EmbarcaTech-2025/projeto-final-antonio_carlos_ricardo/DesenvolvimentoDoProjeto/Fase3/Code/Decode/README.md

# Example:

$ java Decode **07994509EF247AF4976157E876D9C710E1**
- Byte de Controle (BC): 0x07
- Battery: 76.5 %
- Umidade: 34.5 %
- Temperatura: 25.43 °C
- Pressão: 1013.24 hPa
- Latitude: -22.817343 graus
- Longitude: -47.07148 graus
- Altitude: 432.1 m
