EmbarcaTech-2025/projeto-final-antonio_carlos_ricardo/DesenvolvimentoDoProjeto/Fase3/Etapa4/Apresentação 0202.pdf

## Estação Meteorológica IoT

Etapa 4 – Semana 4 – Contexto

- Projeto de estação meteorológica IoT de baixo consumo
- Implantação prevista de 10 unidades no campus
- Comunicação via LoRaWAN
- Backend com TTN e ThingsBoard
- Objetivo da Etapa 4: validação, consolidação e pré-entrega

## Estação Meteorológica IoT

Arquitetura Geral do Sistema

- Nó sensor com microcontrolador RP2040
- Sensores (temperatura, umidade, pressão, GPS)
- Medição de bateria e temperatura do MPU
- Alimentação solar
- Comunicação LoRaWAN
- Gateway FEEC → TTN → ThingsBoard

Arquitetura Geral do Sistema

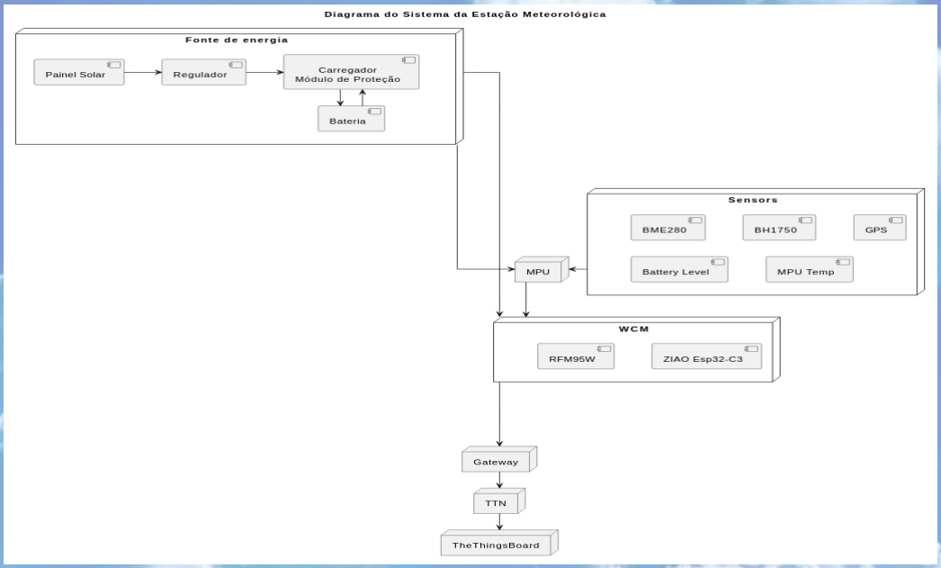
[picture p67: figure]

## Estação Meteorológica IoT

Objetivos e Escopo da Etapa 4

- Validar tecnicamente o protótipo
- Realizar validação externa inicial
- Incorporar feedback técnico e funcional
- Consolidar documentação do projeto
- Preparar o sistema para implantação em campo

## Estação Meteorológica IoT

Validação Técnica e Externa

- Validação técnica interna dos subsistemas
- Testes integrados de sensores, energia e comunicação
- Demonstração do sistema a avaliadores externos

## Estação Meteorológica IoT

Ajustes Realizados no Sistema

- Otimização do payload LoRaWAN
- Melhoria de logs e diagnósticos
- Revisão do gerenciamento energético
- Migração para placa dedicada (PCB própria)

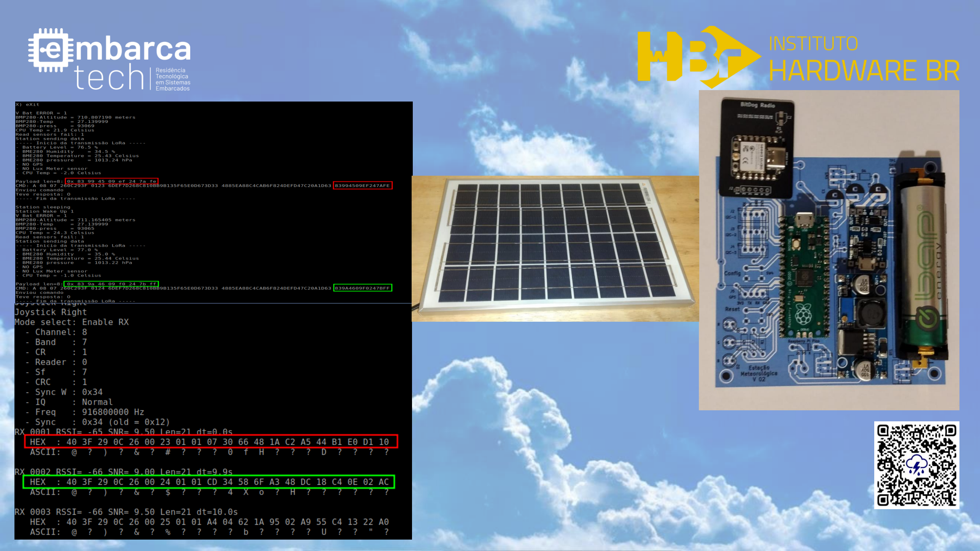
[picture p68: page 7]

## Estação Meteorológica IoT

Evidências de Funcionamento

## - Logs de transmissão LoRaWAN

## - Recepção confirmada no TTN - Testes de carregamento via painel solar

## Estação Meteorológica IoT

Documentação e Organização Final

- Manual do usuário
- Diagramas finais atualizados
- Suporte articulado e disposição mecânica

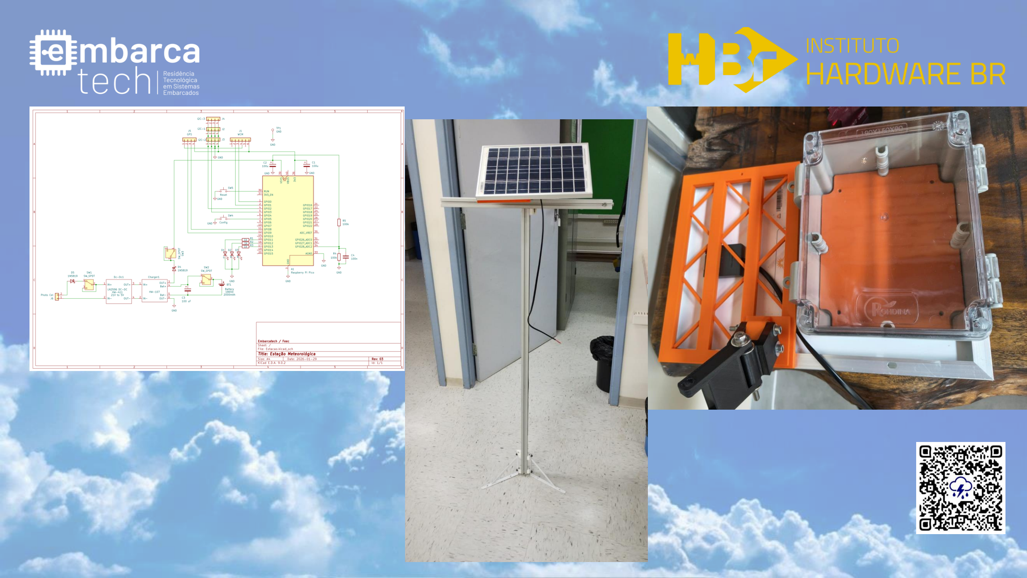
[picture p69: page 10]

## Estação Meteorológica IoT

TRL 5 – Tecnologia validada em ambiente relevante

- O sistema foi validado utilizando infraestrutura real (gateway LoRaWAN e TTN)
- O protótipo opera de forma integrada, cumprindo sua função principal
- Testes energéticos e de comunicação obtiveram sucesso
- A solução encontra-se pronta para implantação piloto, em fase de replicação de unidades

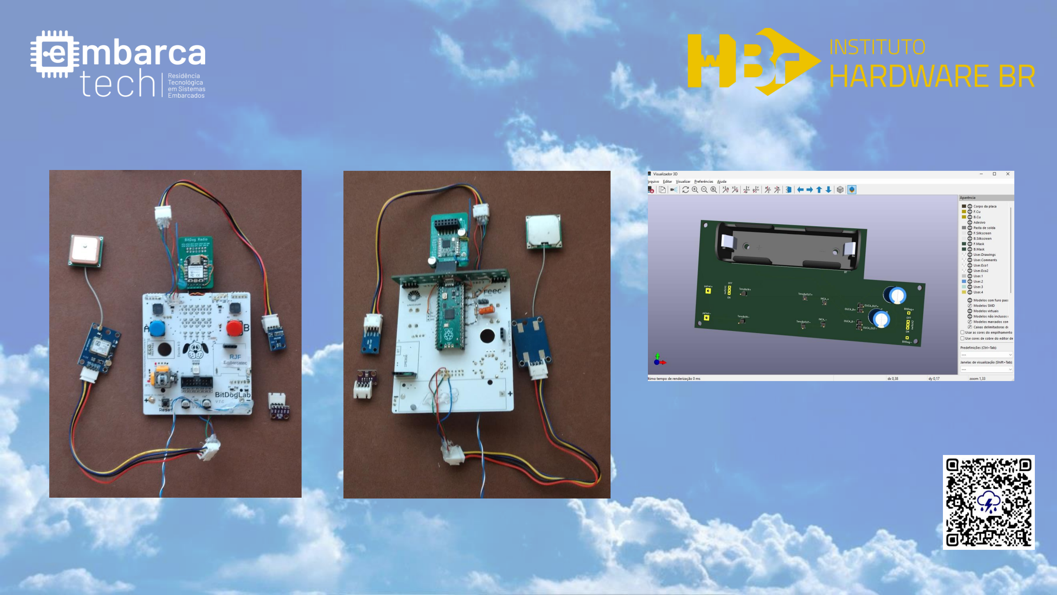
[picture p70: page 12]

## Estação Meteorológica IoT

Em resumo:

- Protótipo validado e documentado
- Sistema pronto para implantação piloto
- Próximo passo: operação contínua em campo

Obrigado!
Perguntas?
