EmbarcaTech-2025/projeto-final-antonio_carlos_ricardo/DesenvolvimentoDoProjeto/Fase3/Etapa3/Apresentação 0501-v2.pdf

Estação Meteorológica IoT
para o Agronegócio e a Agricultura Familiar
- Etapa 3 – Semana 4
- Validação em Campo e Consolidação da Versão Beta
- Antonio Crepaldi – Carlos Perez – Ricardo Furlan

Estação Meteorológica IoT
para o Agronegócio e a Agricultura Familiar
Contexto do Projeto
- Estação meteorológica IoT de baixo consumo
- Implantação de 10 estações no campus da Unicamp
- Comunicação LoRaWAN
- Uso da infraestrutura existente (WCM + Gateway)
- Backend com TTN + ThingsBoard

Estação Meteorológica IoT
para o Agronegócio e a Agricultura Familiar
Objetivos da Semana 4
- Consolidar decisões técnicas da Etapa 3
- Planejar a implantação em escala (10 estações)
- Definir o fluxo de dados ponta a ponta
- Preparar a versão beta para validação em campo
- Organizar documentação e apresentação

Estação Meteorológica IoT
para o Agronegócio e a Agricultura Familiar
Arquitetura da Estação (Nó Sensor)
- BitDogLab (RP2040)
- Sensores meteorológicos
- GPS (UART)
- Módulo WCM (ESP32-C3 + RFM95W)
- Autonomia Energética (placa solar)

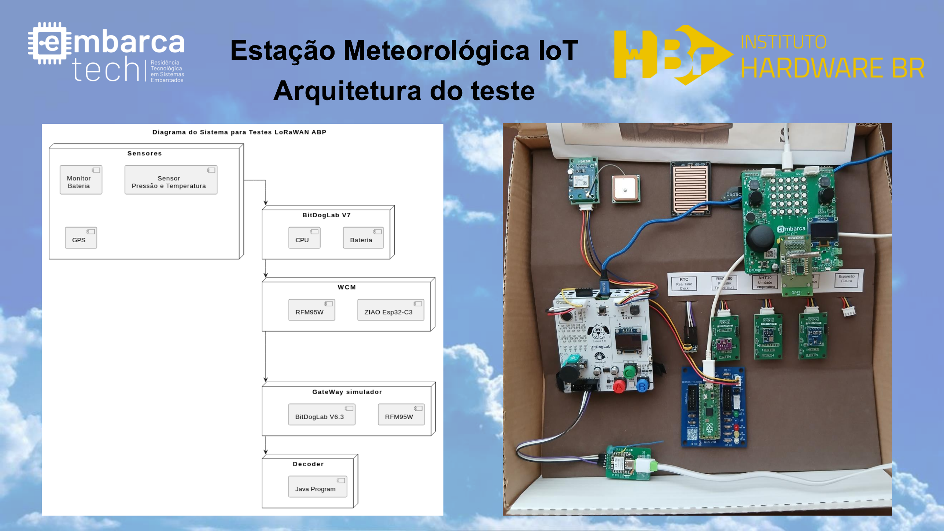
[picture p71: page 5]

Estação Meteorológica IoT
Arquitetura do teste

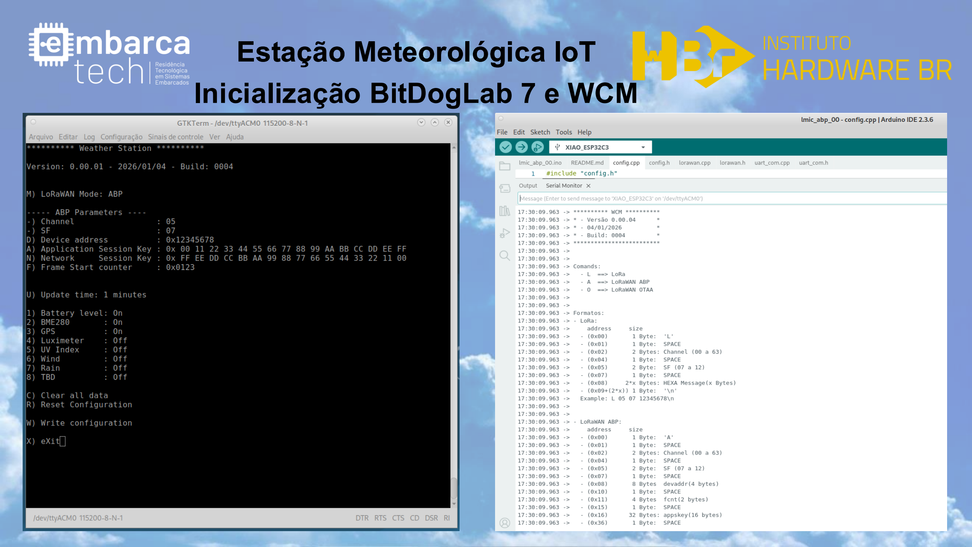
[picture p72: page 6]

Estação Meteorológica IoT
Inicialização BitDogLab 7 e WCM

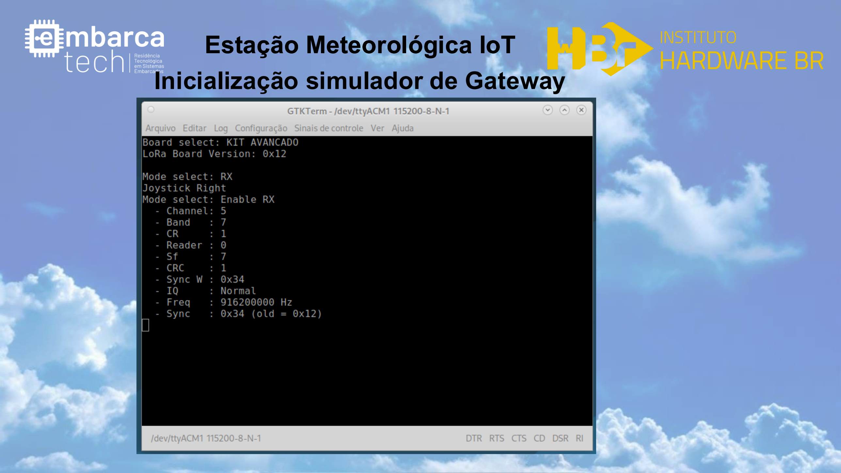
[picture p73: page 7]

Estação Meteorológica IoT
Inicialização simulador de Gateway

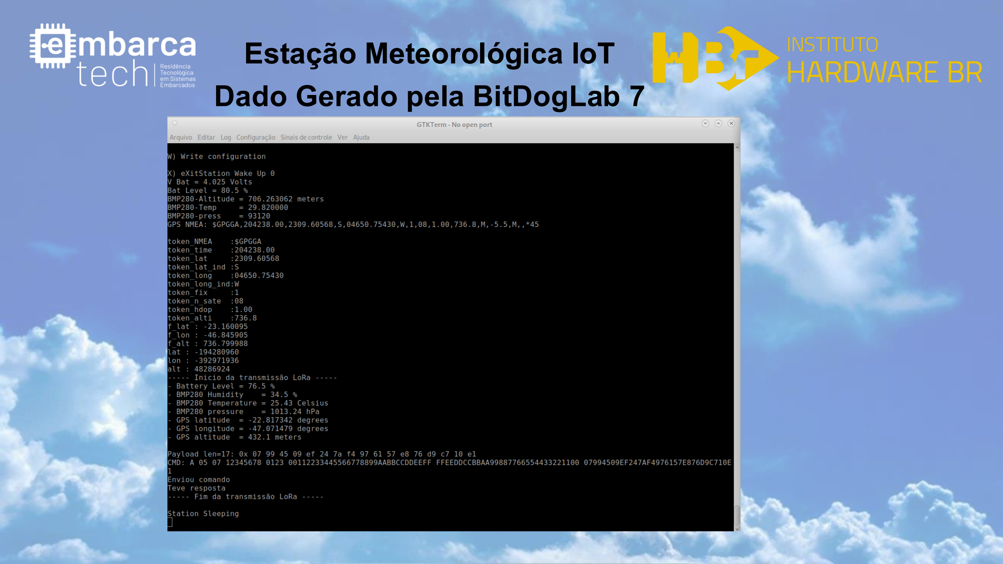
[picture p74: page 8]

Estação Meteorológica IoT
Dado Gerado pela BitDogLab 7

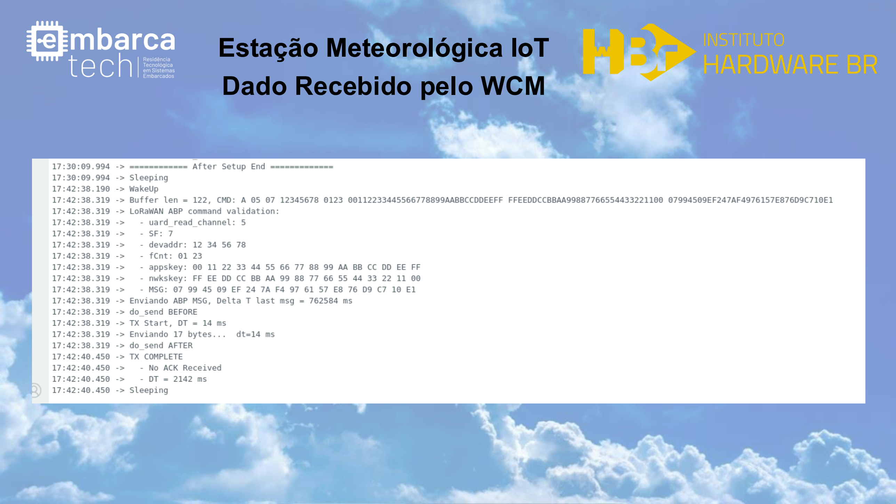
[picture p75: page 9]

Estação Meteorológica IoT
Dado Recebido pelo WCM

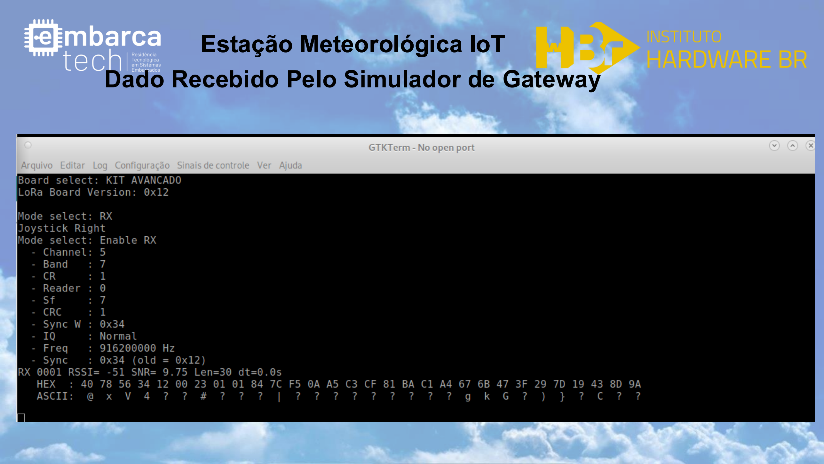
[picture p76: page 10]

Estação Meteorológica IoT
Dado Recebido Pelo Simulador de Gateway

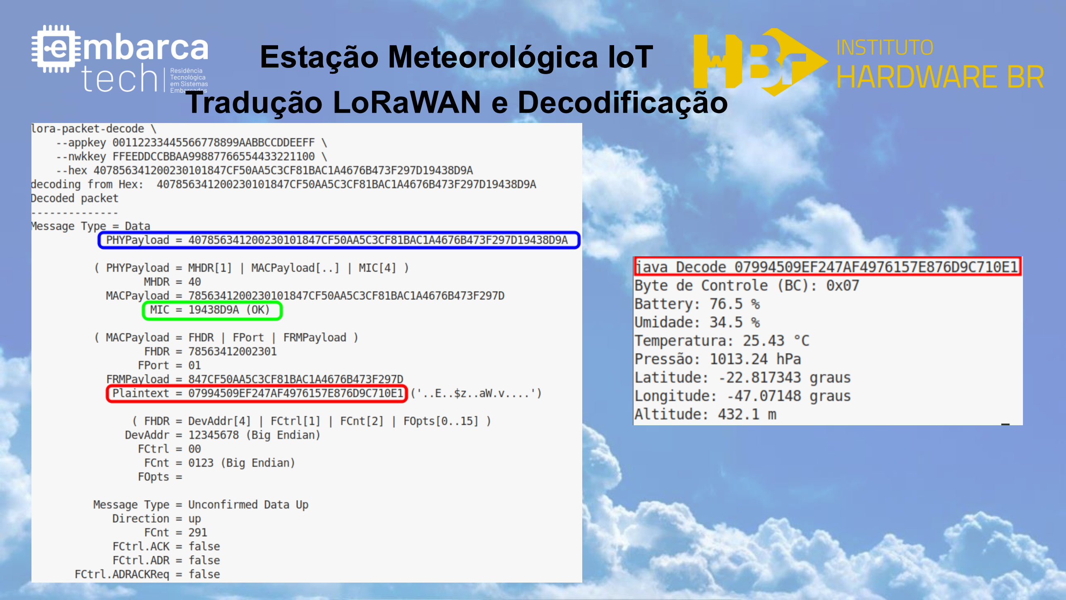
[picture p77: page 11]

Estação Meteorológica IoT
Tradução LoRaWAN e Decodificação

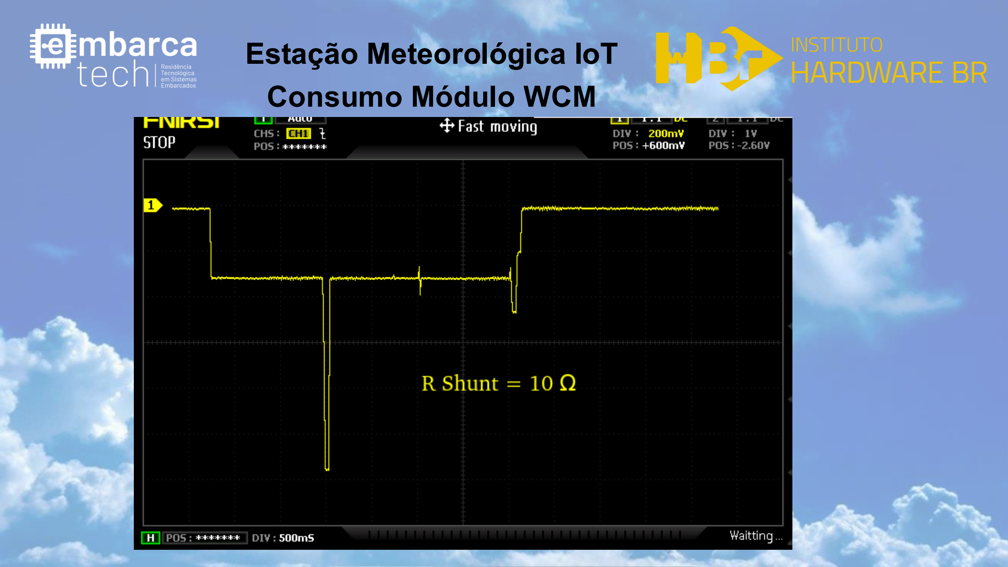
[picture p78: page 12]

Estação Meteorológica IoT
Consumo Módulo WCM

Estação Meteorológica IoT
para o Agronegócio e a Agricultura Familiar

Planejamento da Implantação de 10 Estações

- Identificação única dos End Devices
- Keys exclusivas para cada END DEvice
- Cada Estação será customizada com os sensores apropriados

Estação Meteorológica IoT
para o Agronegócio e a Agricultura Familiar
Dashboards e Visualização
- Plataforma: ThingsBoard
- Dados a sererem exibidos:
- Nível da Bateria
- Temperatura, Umidade e Pressão
- Localização (GPS)
- Status da estação
- Visualização individual e agregada

Estação Meteorológica IoT
para o Agronegócio e a Agricultura Familiar
Consolidação Técnica da Etapa 3
- Comunicação LoRaWAN definida
- Backend padronizado (TTN + ThingsBoard)
- Arquitetura energética solar consolidada
- Estratégias de baixo consumo no RP2040 e WCM
- Payload otimizado para baixo ToA

Estação Meteorológica IoT
para o Agronegócio e a Agricultura Familiar
TRL e Próximos Passos
- TRL atual: 4
- Preparação para TRL 5 com:
- integração física completa
- testes LoRaWAN reais
- validação em campo
- implantação piloto
- Início da Etapa 4

Obrigado!

Estação Meteorológica IoT
para o Agronegócio e a Agricultura Familiar
