EmbarcaTech-2025/projeto-final-antonio_carlos_ricardo/DesenvolvimentoDoProjeto/Fase3/Etapa4/trl_final_etapa4.md

# Análise do TRL Final da Etapa 4 (Pré-Entrega)

## 1. Introdução

O Nível de Maturidade Tecnológica (Technology Readiness Level – TRL) é utilizado para avaliar o grau de desenvolvimento e validação de uma tecnologia ao longo de seu ciclo de vida. Esta seção apresenta a análise do **TRL final alcançado ao término da Etapa 4**, considerando as atividades realizadas, os resultados obtidos e as evidências documentadas ao longo do projeto.

A avaliação tem caráter de **pré-entrega**, ou seja, reflete o estado atual do protótipo imediatamente antes da implantação contínua em campo.

---

## 2. Referência de TRL Utilizada

Para esta análise, adota-se a definição clássica de TRL, com foco nos níveis intermediários:

- **TRL 4:** Tecnologia validada em ambiente de laboratório  
- **TRL 5:** Tecnologia validada em ambiente relevante  
- **TRL 6:** Tecnologia demonstrada em ambiente relevante com operação contínua  

A distinção entre os níveis 5 e 6 é particularmente importante neste projeto.

---

## 3. Evidências Técnicas Disponíveis

Ao final da Etapa 4, o projeto apresenta as seguintes evidências:

- protótipo funcional e integrado (hardware e firmware);
- comunicação LoRaWAN validada com gateway real e The Things Network (TTN);
- transmissão e recepção de dados confirmadas;
- testes de carregamento da bateria via painel solar;
- validação técnica interna concluída;
- validação externa inicial realizada com feedback incorporado;
- documentação técnica e de usuário revisada;
- repositório planejado para versionado;
- diagramas finais atualizados (arquitetura, esquemático e PCB).

Esses elementos caracterizam um sistema funcional além do ambiente puramente laboratorial.

---

## 4. Classificação do TRL Final

Com base nas evidências apresentadas, o projeto é classificado como:

### **TRL 5 – Tecnologia validada em ambiente relevante**

Essa classificação se justifica porque:

- o sistema foi validado utilizando infraestrutura real (gateway LoRaWAN e TTN;
- o protótipo opera de forma integrada, cumprindo sua função principal;
- testes energéticos e de comunicação foram realizados fora de simulações;
- usuários externos ao grupo avaliaram o sistema e forneceram feedback;
- a solução encontra-se pronta para implantação piloto.
