EmbarcaTech-2025/projeto-final-antonio_carlos_ricardo/DesenvolvimentoDoProjeto/Fase3/Etapa1_Semana1/Modelo_Negocios.md

### **Proposta de Valor**

#### **1. O Cenário Atual: O Dilema dos Dados Climáticos**

Gestores e operadores em diversos setores sabem que a previsão do tempo geral raramente reflete as condições de um ponto específico. Essa discrepância gera um dilema claro, validado por análises de mercado, que limita a tomada de decisão:

* **Dados Públicos: Gratuitos, mas Insuficientes.** As estações de órgãos governamentais são essenciais para uma visão regional, mas sua baixa densidade geográfica as torna imprecisas para a gestão de operações locais. Elas não capturam os microclimas — as variações críticas de vento, chuva e temperatura — que podem impactar a segurança e a eficiência de um projeto ou serviço.

* **Soluções Comerciais: Precisas, mas Restritivas.** Para obter dados hiperlocais, o mercado oferece equipamentos de alta tecnologia. No entanto, a maioria opera em um modelo de serviço (MaaS - *Monitoring-as-a-Service*), que vincula o cliente a assinaturas mensais. Isso transforma um investimento em tecnologia em um custo operacional recorrente e, crucialmente, muitas vezes retém a propriedade dos dados com o fornecedor, criando uma forte dependência.

O tomador de decisão fica preso entre um dado gratuito que não é confiável para sua localidade e um dado confiável que gera custos permanentes e limita sua autonomia.

#### **2. Nossa Solução: Acesso à Tecnologia, com Autonomia para o Cliente**

Nossa proposta quebra esse ciclo, oferecendo uma solução que combina precisão e autonomia. Desenvolvemos uma rede de estações meteorológicas de baixo custo e alta performance (baseadas em MCUs com conectividade LoRa, Wi-Fi e BLE), projetada sobre três pilares fundamentais:

* **Investimento Único, Custo Previsível:** Eliminamos o modelo de assinatura. O cliente adquire o hardware em um investimento único, transformando a incerteza de um custo operacional em um ativo fixo e previsível. A ferramenta é sua, sem taxas recorrentes.

* **Precisão no Nível do Ponto de Interesse:** O baixo custo do equipamento permite a instalação de múltiplos sensores em uma área de operação. Isso cria um mapa climático detalhado e em tempo real, fornecendo dados específicos para um bairro crítico, um canteiro de obras, um trecho de rodovia ou um parque industrial.

* **Soberania sobre os Dados:** Este é o nosso principal diferencial. Os dados coletados são de propriedade exclusiva do cliente. Eles podem ser armazenados e analisados localmente ou integrados a qualquer sistema de gestão via API, garantindo total liberdade e controle sobre a informação estratégica de sua operação.

#### **3. Um Comparativo Direto de Modelos**

| Característica | Rede Pública (Ex: INMET) | Soluções por Assinatura | **Nossa Proposta** |
| :--- | :--- | :--- | :--- |
| **Modelo de Custo** | Gratuito | Custo Operacional Recorrente | **Investimento Único** |
| **Granularidade dos Dados**| Muito Baixa (Regional) | Alta (Nível da propriedade) | **Altíssima (Nível do local/bairro)** |
| **Propriedade dos Dados**| Dados Públicos | Do Fornecedor / Compartilhada | **100% do Cliente** |
| **Autonomia Tecnológica** | Total | Baixa (Dependência da plataforma) | **Total (Dados abertos e integráveis)** |

#### **4. Transformando Dados em Decisões Estratégicas**

Com acesso a dados hiperlocais e proprietários, a gestão passa da reatividade para a proatividade:

* **Otimizar a alocação de recursos:** Gerenciar equipes de emergência, frotas de veículos ou o consumo de água e energia com base em condições reais e iminentes.
* **Aumentar a segurança operacional:** Interromper operações de risco (como içamento em construções) com base em alertas de vento, ou evacuar áreas com base em previsões de chuvas intensas.
* **Mitigar riscos e prevenir perdas:** Emitir alertas de desastres altamente localizados, proteger ativos sensíveis ao clima e otimizar rotas logísticas para evitar zonas de intempéries.
* **Construir inteligência operacional:** Criar um histórico de dados robusto e proprietário para analisar tendências, aprimorar o planejamento urbano, logístico ou de projetos futuros.

#### **5. Indicadores de Sucesso**
Nosso sucesso não está apenas na tecnologia, mas no resultado real que ela gera. Por isso, focamos em indicadores simples e claros que mostram se estamos no caminho certo.

| O que vamos medir | Nossa Meta |
| :--- | :--- |
| **Facilidade** | Que qualquer pessoa consiga instalar o equipamento em menos de 30 minutos, e ele deva funcionar 99% do tempo sem falhas. |
| **Retorno do Investimento** | Que o equipamento se pague em menos de 2 anos, seja pela economia que gera ou pelas perdas que ajudará a evitar. |
| **Satisfação do Cliente** | Que tenhamos clientes que não apenas continuam usando nossa solução, mas que a recomendam para outros. |
