EmbarcaTech-2025/projeto-final-antonio_carlos_ricardo/DesenvolvimentoDoProjeto/Fase3/Etapa1_Semana1/questionario_cliente.md

# Questionário de Levantamento de Requisitos  
### Projeto: Estação Meteorológica IoT  
**Fase 3 – Entrevista com o Usuário/Cliente**

---

## 1. Identificação do Entrevistado
- **Nome:**  Rafitcha
- **Cargo/Função:**  Monitor do Projeto/Cliente
- **Área de atuação:**  Monitoria Embarcatech
- **Data da entrevista:** Data da entrevista
- **Entrevistador:** Entrevistador  

---

## 2. Uso Atual e Expectativas

1. Você já utiliza algum tipo de estação meteorológica ou sensor ambiental?  
   - ( ) Não  
   - ( ) Sim
     - quais modelos tipos: ______________________________________________
     - quais limitações você encontrou no sistema que utilizou:___________

1. Quais são as **principais informações meteorológicas** que você considera mais importantes monitorar?  
   - ( ) Temperatura  
   - ( ) Umidade do ar  
   - ( ) Pressão atmosférica  
   - ( ) Velocidade do vento  
   - ( ) Direção do vento  
   - ( ) Pluviosidade  
   - ( ) Luminosidade  
   - ( ) Outras: ___________________________________________________

1. Com que **frequência** você gostaria que fosse feita a **coleta dos dados**?  
   - A cada ____ (Segundos, minutos , horas)
   - ( ) Outro intervalo: ____________________________
   
1. Com que **frequência** você gostaria que as medições fossem **atualizadas**?  
   - ( ) Em tempo real  
   - ( ) A cada minuto  
   - ( ) A cada hora  
   - ( ) Outro intervalo: ____________________________

1. Qual seria a **forma ideal de visualizar os dados**?  
   - ( ) Display local na estação  
   - ( ) Display remoto dedicado a estação
   - ( ) Aplicativo Celular
   - ( ) Site Web 
   - ( ) Relatórios automáticos enviados via:
     - ( ) Whatsapp
     - ( ) Telegrama
     - ( ) e-mail
     - ( ) Outro: _____________________________
   - ( ) Outro: ____________________________

---

## 3. Funcionalidades Desejadas

1. Deseja que a estação **envie alertas automáticos** (ex.: chuva forte, temperatura extrema, falha no sensor)? 
   - ( ) Não  
   - ( ) Sim, como gostaria de recebê-los? (ex.: e-mail, app, WhatsApp): _________________

1. Acha importante **armazenar o histórico dos dados** para consultas futuras e gráficos de tendência?  
   - ( ) Não 
   - ( ) Sim, por quanto tempo: ______________ 

1. Você considera útil a possibilidade de **exportar os dados** (CSV, Excel, etc.)? 
   - ( ) Não  
   - ( ) Sim, qual formato: ___________________________________

1. Há interesse em fazer análise comparativa entre estações ou que fosse feito a média entre **várias estações** (por exemplo, em diferentes áreas da propriedade)?
   - ( ) Não  
   - ( ) Sim, descrever: ________________________

---

## 4. Requisitos Técnicos e Operacionais

1. Em relação à **conectividade**, quais opções são mais viáveis no seu ambiente?  
   - ( ) Cabeada(Ethernet, USB, RS232 etc)
   - ( ) Bluetooth
   - ( ) Wi-Fi  
   - ( ) 4G/5G  
   - ( ) LoRa  
   - ( ) Zibgee
   - ( ) Outro: ____________________________

1. Qual (ou quais) deve ser a **fonte energética primária** da estação?
   - ( ) Alimentação elétrica contínua  
   - ( ) Bateria  
   - ( ) Energia solar  
   - ( ) Outro: ____________________________

1. Deve haver fonte auxiliar, no-brake/bateria?
   - ( ) Não
   - ( ) Sim, qual o tempo de duração mínimo: __________________________
 
1. Há restrições quanto à **instalação física** (local, tamanho, tipo de fixação)?
   - ( ) Não
   - ( ) Sim, qual/quais:___________________________________________

1. Em caso de falha de conexão como o servidor, é importante que os dados sejam **armazenados localmente** e enviados depois?  
   - ( ) Não
   - ( ) Sim, qual o intervalo mínimo de armazenamento desses dados: _________

---

## 5. Interface e Usabilidade

1. Quais informações você gostaria que aparecessem **no display local** (caso exista)?  
   - ( ) Temperatura e umidade  
   - ( ) Data e hora  
   - ( ) Status da rede  
   - ( ) Alertas e avisos  
   - ( ) Outro: ____________________________

1. Você prefere uma interface de configuração:  
   - ( ) Por menu no display  
   - ( ) Via navegador web  
   - ( ) Via aplicativo móvel
   - ( ) Outro: ____________________________  

1. A interface do protótipo atual (menu e configurações) é clara e intuitiva?
   - ( ) Sim
   - ( ) Parcialmente
   - ( ) Não  
   - Sugestões de melhoria: ____________________________

---

## 6. Casos de Uso

1. Em quais **situações práticas** você imagina usar a estação meteorológica? 
    :___________________________________________

1. Descreva um **exemplo real** de como as informações coletadas ajudariam no seu trabalho ou decisão.  
    :___________________________________________

1. Há algum cenário onde o sistema **deveria ter um funcionamento diferenciado ou comportamento especial** (ex.: modo de economia, tempestades, ausência de rede)?  
    :___________________________________________

---

## 7. Considerações Finais

1. O que você considera **mais importante** para o sucesso desse projeto?  
    :___________________________________________

1. Deseja sugerir **novos sensores ou recursos** para futuras versões?  
    :_____________________________________________
