EmbarcaTech-2025/projeto-final-antonio_carlos_ricardo/DesenvolvimentoDoProjeto/Etapa4/Apresentação 0809c.pptx

Estação Meteorológica para o Agronegócio e a Agricultura Familiar

- Problema: incerteza climática.
- Solução: informação a partir de dados localizados.
- Objetivo: desenvolver uma estação meteorológica inteligente, escalável, autônoma, modular e de baixo custo, fornecendo dados precisos, localizados e em tempo real de temperatura, umidade do ar e do solo, pressão atmosférica e outros.
- Requisitos: coleta, armazenamento, transmissão e visualização de dados climáticos.

## Slide 2

Componentes da Estação Meteorológica


## Slide 3

Estrutura de comunicação
entre os núcleos

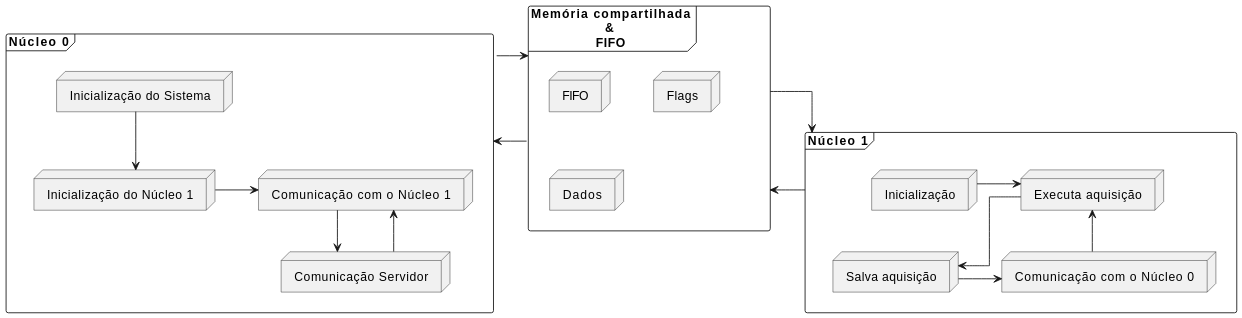
[picture p119: figure]

## Slide 4

Mapa Memória Flash

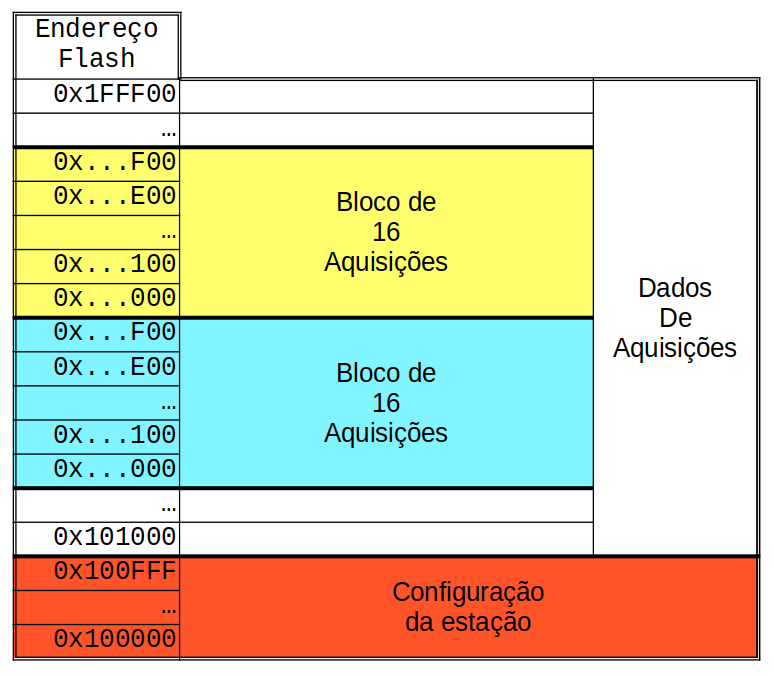
[picture p120: figure]

Dados da aquisição

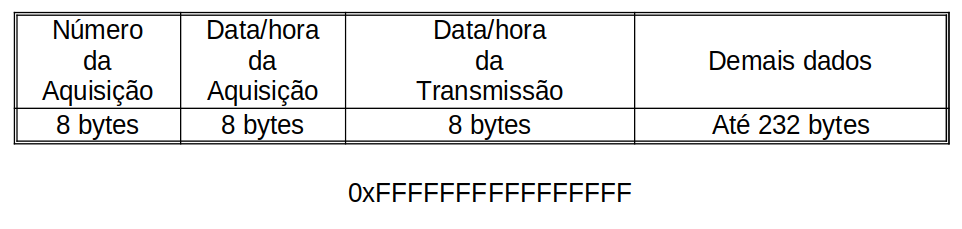
[picture p121: figure]

## Slide 5

Estrutura do Servidor

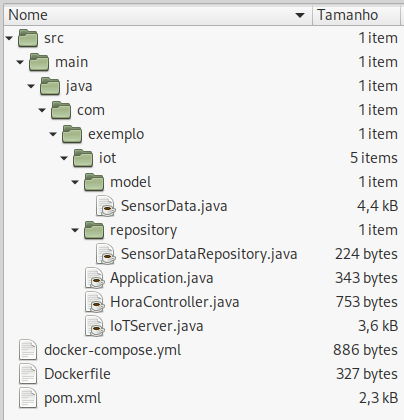
[picture p122: figure]

Principais Comandos

- $ docker-compose build
- $ docker-compose up

## Slide 6

Visualização de Dados da Estação

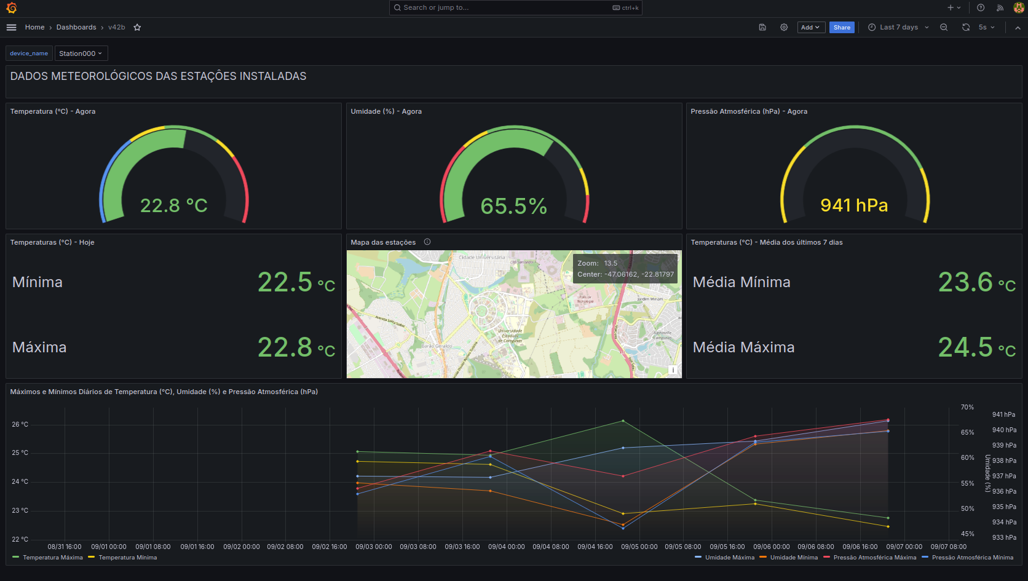
[picture p123: figure]

## Slide 7

Estação Meteorológica para o Agronegócio e a Agricultura Familiar

Obrigado!
