EmbarcaTech-2025/projeto-final-antonio_carlos_ricardo/apresentacao_Pitch_2302.pdf

# Estação Meteorológica IoT

Monitoramento ambiental distribuído ainda não é amplamente difundido
- Áreas agrícolas
- Campi universitários (pesquisa)
- Cidades inteligentes
- Custo de estações comerciais ~ R$ 1.390+

# Estação Meteorológica IoT

Estação Meteorológica IoT de Baixo Custo, Baixo Consumo e Longo Alcance
- Comunicação LoRaWAN
- Energia Solar
- Estação:
- Autônoma
- Modular
- Escalável

# Estação Meteorológica IoT

Solução Implementada
- Estação
- Gateway
- The Things Network (TTN)
- The Things Board

# Estação Meteorológica IoT

Diferenciais Competitivos
- Hardware dedicado (baixo consumo real)
- Payload otimizado (menor ToA) e menor consumo
- Escalável para múltiplas estações
- IP68
- Projeto open source
- Custo de montagem acessível

# Estação Meteorológica IoT

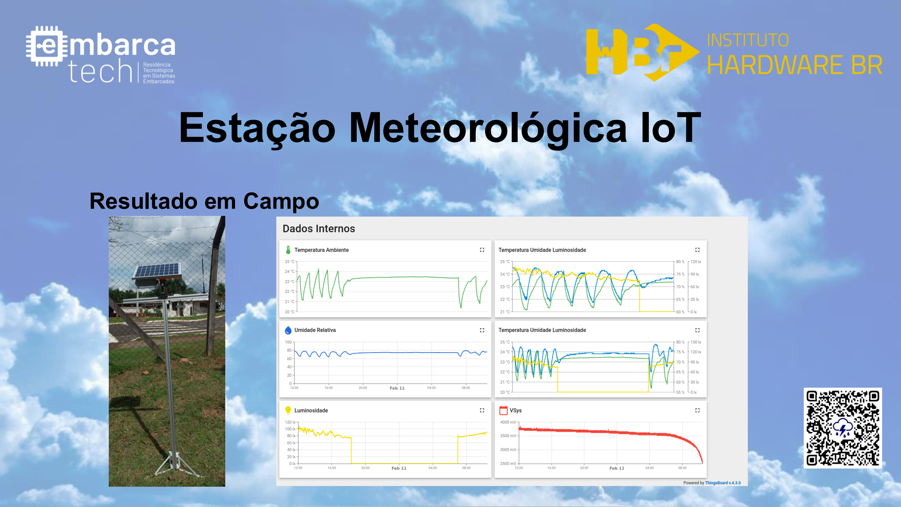
[picture p125: page 5]

Resultado em Campo
