EmbarcaTech-2025/projeto-final-antonio_carlos_ricardo/DesenvolvimentoDoProjeto/Fase3/Etapa5/Etapa 5 - Acompanhamento semanal2.pdf

## Etapa 5 - Acompanhamento semanal

Data: 15/02/2026
Projeto: Estação Meteorológica IoT
Integrantes: Antonio Crepaldi – Carlos Perez – Ricardo Fulan
- O que falta até 23/fev (entrega final)?
Até 23/02 faltam as seguintes atividades:
- Montagem final de unidades
- Consolidação de repositório independente
- Acompanhamento do funcionamento contínuo de múltiplas estações em campo
- Revisão e correção da documentação final
- O que foi feito no último sprint? (por integrante)
- Todos: Documentação final do projeto
- Antonio e Carlos: Testes de recepção LoRaWAN
- Todos: Organização do repositório para entrega final
- Todos: Montagem de protótipos
- Ricardo: Montagem da terceira PCB
- Ricardo: Otimização de código da estação
- O que será feito no próximo sprint? (por integrante)
- Todos: Montagem final de unidades
- Todos: Consolidação de repositório independente
- Todos: Acompanhamento do funcionamento contínuo de múltiplas estações em campo
- Todos: Revisão e correção da documentação final
- Todos: Entrega Final
- Todos: Apresentação Final
- Houve algum impeditivo recente?

Sim, queda da plataforma TheThingsBoard por 6 horas. Atraso na confecção da PCB revisada na FEEC.

- Como está a aderência ao cronograma? Há riscos em vista?

Sem problemas. Não há riscos em vista.
