EmbarcaTech-2025/projeto-final-antonio_carlos_ricardo/DesenvolvimentoDoProjeto/Fase3/Etapa5/Etapa5-Acompanhamento semanal.pdf

## Etapa 5 - Acompanhamento semanal

Data: 08/02/2026
Projeto: Estação Meteorológica IoT
Integrantes: Antonio Crepaldi – Carlos Perez – Ricardo Fulan
- O que falta até 23/fev (entrega final)?
Até 23/02 faltam as seguintes atividades:
- Revisão da documentação
- Montagem final das estações para instalação
- Criação dos dashboards
- Criação do repositório do projeto
- Validação final
- O que foi feito no último sprint? (por integrante)
- Ricardo: montagem dos protótipos, correção do esquemático/PCB, correção do problema do carregador.
- Carlos: Montagem mecânica do primeiro protótipo, apresentação na HBR, validação da comunicação do protótipo, planejamento do repositório.
- Antonio: Apresentação na HBR. Montagem mecânica do primeiro protótipo, ensaios com carregador e placa solar.
- O que será feito no próximo sprint? (por integrante)
- Ricardo: Documentação do código, documentação do projeto, repositório, montagem das novas estações.
- Carlos: Documentação do projeto, repositório, instalação das estações, criação de dashboards.
- Antonio: Documentação do projeto, repositório, instalação das estações, trocar carregador do primeiro proiótipo.
- Houve algum impeditivo recente?

Sim, atrasos em confecção de placas, dedetização do lab, troca de servidor para TheThingsBoard, componentes com defeito (carregador e Raspberry Pi Pico).

- Como está a aderência ao cronograma? Há riscos em vista?

A necessidade de entregar o projeto com uma semana de antecedência, impacta o cronograma previamente planejado. Sim, há riscos. Se algum imprevisto ocorrer, a entrega será afetada.
