EmbarcaTech-2025/projeto-final-antonio_carlos_ricardo/DesenvolvimentoDoProjeto/Fase3/Etapa5/Etapa5-Planejamento Inicial.pdf

Atividade | Responsável | Prazo | Status e data

### 1. Construção e Montagem das Estações

Montagem do primeiro protótipo em campo | Antonio/Carlos/Ricardo | 02/02/2026
Correção do esquemático/layout da PCB | Ricardo | 04/02/2026
Execução de placas PCB atualizadas | Ricardo/Fruett | 09/02/2026
Investigação e correção dos problemas no sistema de
carregamento | Ricardo/Carlos | 09/02/2023
Montagem eletrônica das novas placas | Todos | 09/02/2026
Testes elétricos e funcionais das placas | Antonio/Carlos | 09/02/2026
Testes de comunicação LoRaWAN | Carlos | 09/02/2026
Montagem mecânica de mais 2 estações | Todos | 09/02/2026
Montagem de 4 estações operacionais | Todos | 15/02/2026
Substituição de diodos Zener nas placas existentes | Ricardo | 09/02/2026
Troca do circuito carregador na estação já instalada | Antonio | 09/02/2026

### 2. Instalação em Campo

Definição dos locais de instalação no campus | Antonio/CarlosFruett | 09/02/2026
Instalação das estações distribuídas | Todos | 15/02/2026
Teste de alcance pelo campus | Antonio/Carlos | 09/02/2026
Verificação de funcionamento após instalação | Todos | 15/02/2026

### 3. Dashboards e Backend

Verificação da chegada de dados no ThingsBoard | Carlos | 15/02/2026
Verificação da persistência e histórico dos dados | Carlos | 15/02/2026
Criação dos dashboards | Carlos | 15/02/2026
Publicação dos dashboards para visualização | Carlos | 15/02/2026

### 4. Repositório Open Source

Criação de repositório exclusivo open source | Todos | 15/02/2026
Elaboração do README principal do projeto | Todos | 15/02/2026

### 5. Documentação

Revisão e finalização do manual do usuário | Todos | 15/02/2026
Elaboração do manual de construção da estação | Todos | 15/02/2026

Elaboração do manual de instalação: | Todos | 15/02/2026
Gateway | Grupo WCM | 15/02/2026
The Things Network (TTN) | Grupo WCM | 15/02/2026
ThingsBoard | Grupo WCM | 15/02/2026
Revisão e documentação de todo o código-fonte:
Firmware RP2040 | Ricardo | 15/02/2026
Firmware WCM | Ricardo | 15/02/2026

### 6. Validação Final

Testes integrados das estações completas | Todos | 15/02/2026
Coleta de evidências finais de funcionamento | Todos | 15/02/2026
Entrega |Final e Apresentação | Todos | 15/02/2026
