EmbarcaTech-2025/projeto-final-antonio_carlos_ricardo/DesenvolvimentoDoProjeto/Etapa2/assets/fluxograma.png

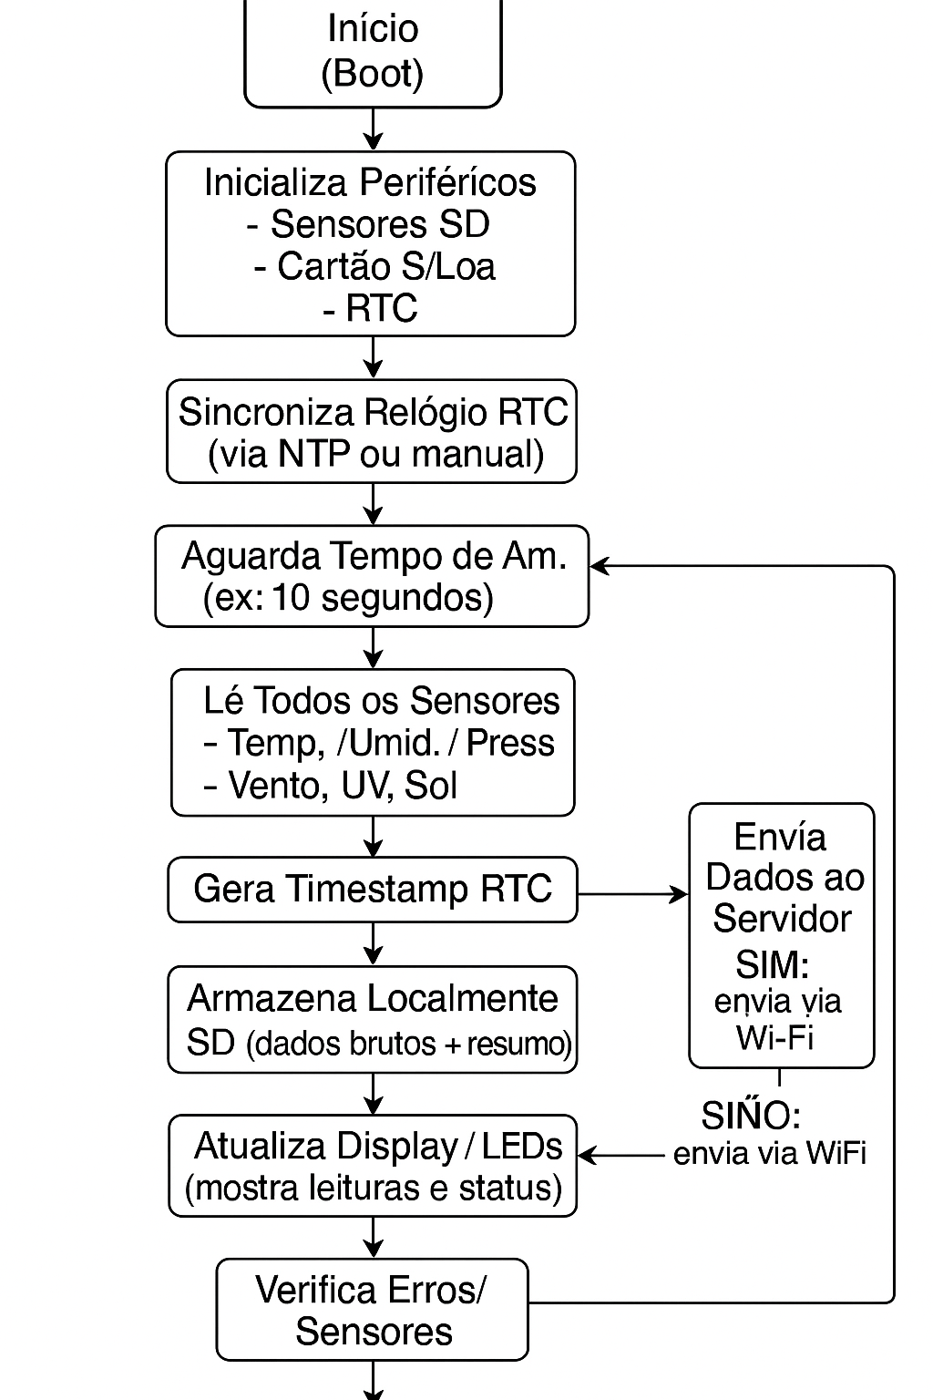
DesenvolvimentoDoProjeto/Etapa2/assets/fluxograma.png
