EmbarcaTech-2025/projeto-final-antonio_carlos_ricardo/DocumentacaoFinalDoProjeto/Software/Main_Board/docs/html/buttons__and__leds_8c__incl.png

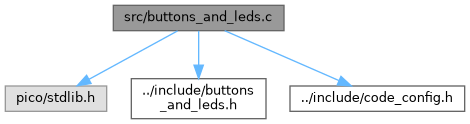
DocumentacaoFinalDoProjeto/Software/Main_Board/docs/html/buttons__and__leds_8c__incl.png
