EmbarcaTech-2025/projeto-final-antonio_carlos_ricardo/DocumentacaoFinalDoProjeto/Software/Main_Board/docs/html/est__config_8h__dep__incl.png

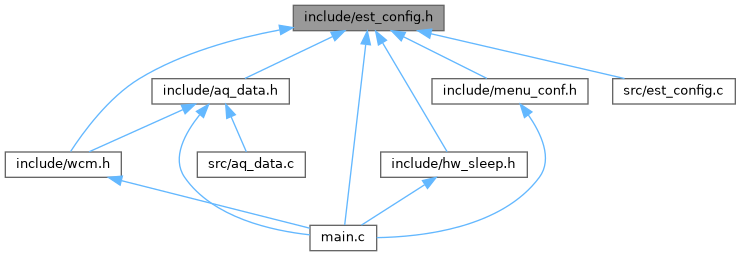
DocumentacaoFinalDoProjeto/Software/Main_Board/docs/html/est__config_8h__dep__incl.png
