EmbarcaTech-2025/projeto-final-antonio_carlos_ricardo/DocumentacaoFinalDoProjeto/Software/Main_Board/docs/html/hw__sleep_8h__incl.png

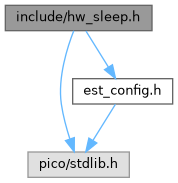
DocumentacaoFinalDoProjeto/Software/Main_Board/docs/html/hw__sleep_8h__incl.png
