EmbarcaTech-2025/projeto-final-antonio_carlos_ricardo/DesenvolvimentoDoProjeto/Etapa4/CODE_estacao_meteorologica_01/include/core1_data.h

/**
 * @file    core1_data.h
 * @author  Carlos e Ricardo
 * @brief   Define a variavel EstationData que é utilizada no Core1 para aquisição de dados
 * @version 0.1
 * @date    2025-09-05
 * 
 * @copyright Copyright (c) 2025
 */
#ifndef CORE1_DATA_H
#define CORE1_DATA_H

#include "estation_data.h"

/**
 * @brief Variavel EstationData que é utilizada no Core1 para aquisição de dados
 * 
 */
extern EstationData core1_estation_data;

#endif // CORE1_DATA_H
