EmbarcaTech-2025/projeto-final-antonio_carlos_ricardo/DesenvolvimentoDoProjeto/Etapa4/CODE_estacao_meteorologica_01/include/testes.h

/**
 * @file    testes.h
 * @author  Carlos e Ricardo
 * @brief   Rotinas para testes de acesso aos sensores I2C
 * @version 0.1
 * @date    2025-09-16
 * 
 * @copyright Copyright (c) 2025
 */
#ifndef TESTES_H
#define TESTES_H

/**
 * @brief   Rotinas para testes de acesso aos sensores I2C
 * 
 */
void testes_i2c();


#endif // TESTES_H
